newmatik-old/uno/UNO-TH_Rev3e_3D-Model_Collada/model/Image1.jpg

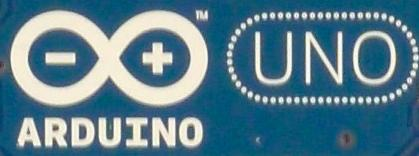
UNO-TH_Rev3e_3D-Model_Collada/model/Image1.jpg
