newmatik-old/uno/UNO-TH_Rev3e_3D-Model_Collada/model/PB1_3.JPG

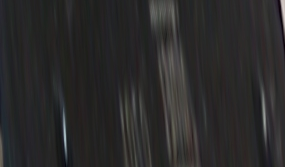
UNO-TH_Rev3e_3D-Model_Collada/model/PB1_3.JPG
